jasminpatry/boostino/gaugeFg.c

#include "gaugeFg.h"

const uint16_t g_aNBbGaugeFg[] = { 10, 9, 311, 225 };
const uint8_t g_aBGaugeFg[] = {
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
};
