jasminpatry/boostino/labelAfr.c

#include "labelAfr.h"

const uint16_t g_aNBbLabelAfr[] = { 75, 9, 102, 21 };
const uint8_t g_aBLabelAfr[] = {
	0x0, 0x0, 0x0, 0x0, 0x1b, 0x66, 0x66, 0x2f, 0x0, 0x0, 0x0, 0x0, 0x2f, 0x66, 0x66, 0x66, 0x66, 0x66, 0x0, 0x55, 0x66, 0x66, 0x66, 0x66, 0x55, 0x0, 0x0,
	0x0, 0x0, 0x0, 0x0, 0xb6, 0xff, 0xff, 0x97, 0x0, 0x0, 0x0, 0x66, 0xf1, 0xff, 0xff, 0xff, 0xff, 0xff, 0x1b, 0xe3, 0xff, 0xff, 0xff, 0xff, 0xff, 0x87, 0x0,
	0x0, 0x0, 0x0, 0x43, 0xff, 0xf1, 0xff, 0xb6, 0x0, 0x0, 0x0, 0xd3, 0xff, 0xc5, 0x96, 0x97, 0x97, 0x87, 0x1b, 0xff, 0xff, 0x97, 0x97, 0xb6, 0xff, 0xf1, 0x0,
	0x0, 0x0, 0x0, 0xb6, 0xff, 0x87, 0xff, 0xd4, 0x0, 0x0, 0x1b, 0xff, 0xff, 0x43, 0x0, 0x0, 0x0, 0x0, 0x66, 0xff, 0xe2, 0x0, 0x0, 0x42, 0xff, 0xff, 0x1a,
	0x0, 0x0, 0x43, 0xff, 0xe3, 0x1a, 0xff, 0xff, 0x1a, 0x0, 0x42, 0xff, 0xff, 0x1b, 0x0, 0x0, 0x0, 0x0, 0x77, 0xff, 0xd3, 0x0, 0x0, 0x76, 0xff, 0xe3, 0x0,
	0x0, 0x0, 0xa6, 0xff, 0x87, 0x0, 0xe2, 0xff, 0x2f, 0x0, 0x66, 0xff, 0xff, 0xd4, 0xd4, 0xd4, 0xa6, 0x0, 0x96, 0xff, 0xc5, 0x97, 0x97, 0xe2, 0xff, 0x97, 0x0,
	0x0, 0x1a, 0xf1, 0xf0, 0x1b, 0x1a, 0xd3, 0xff, 0x66, 0x0, 0x87, 0xff, 0xff, 0xff, 0xff, 0xff, 0x97, 0x0, 0xc4, 0xff, 0xff, 0xff, 0xff, 0xff, 0x97, 0x0, 0x0,
	0x0, 0x97, 0xff, 0xff, 0xff, 0xff, 0xff, 0xff, 0x87, 0x0, 0xa6, 0xff, 0x97, 0x1a, 0x1b, 0x1a, 0x0, 0x0, 0xd4, 0xff, 0x87, 0x66, 0xf1, 0xff, 0x42, 0x0, 0x0,
	0x1a, 0xf0, 0xff, 0xd3, 0xd4, 0xd4, 0xe2, 0xff, 0x97, 0x0, 0xd4, 0xff, 0x77, 0x0, 0x0, 0x0, 0x0, 0x1a, 0xff, 0xff, 0x2f, 0x0, 0xb6, 0xff, 0x87, 0x0, 0x0,
	0x97, 0xff, 0xb5, 0x0, 0x0, 0x0, 0x87, 0xff, 0xd3, 0x0, 0xf1, 0xff, 0x55, 0x0, 0x0, 0x0, 0x0, 0x55, 0xff, 0xf1, 0x0, 0x0, 0x87, 0xff, 0xc5, 0x0, 0x0,
	0xf0, 0xff, 0x43, 0x0, 0x0, 0x0, 0x66, 0xff, 0xe2, 0x1b, 0xff, 0xff, 0x1a, 0x0, 0x0, 0x0, 0x0, 0x66, 0xff, 0xd4, 0x0, 0x0, 0x42, 0xff, 0xff, 0x1b, 0x0,
	0x1b, 0x1b, 0x0, 0x0, 0x0, 0x0, 0x0, 0x1b, 0x1a, 0x0, 0x1b, 0x1a, 0x0, 0x0, 0x0, 0x0, 0x0, 0x0, 0x1b, 0x0, 0x0, 0x0, 0x0, 0x1a, 0x1b, 0x0, 0x0,
};
