jasminpatry/boostino/labelMph.c

#include "labelMph.h"

const uint16_t g_aNBbLabelMph[] = { 71, 9, 102, 21 };
const uint8_t g_aBLabelMph[] = {
	0x0, 0x0, 0x0, 0x66, 0x66, 0x0, 0x0, 0x0, 0x0, 0x1b, 0x66, 0x54, 0x0, 0x0, 0x55, 0x66, 0x66, 0x66, 0x66, 0x55, 0x0, 0x0, 0x1a, 0x66, 0x54, 0x0, 0x0, 0x0, 0x1b, 0x66, 0x54, 
	0x0, 0x0, 0x66, 0xff, 0xff, 0x1a, 0x0, 0x0, 0x0, 0xb6, 0xff, 0xd4, 0x0, 0x0, 0xe2, 0xff, 0xff, 0xff, 0xff, 0xff, 0xa7, 0x0, 0x87, 0xff, 0xd3, 0x0, 0x0, 0x0, 0x87, 0xff, 0xc5, 
	0x0, 0x0, 0xa6, 0xff, 0xff, 0x65, 0x0, 0x0, 0x43, 0xff, 0xff, 0x97, 0x0, 0x1b, 0xff, 0xff, 0x97, 0x97, 0xb5, 0xff, 0xff, 0x1b, 0x97, 0xff, 0x97, 0x0, 0x0, 0x0, 0x97, 0xff, 0x97, 
	0x0, 0x0, 0xd4, 0xff, 0xff, 0x76, 0x0, 0x0, 0xb6, 0xff, 0xff, 0x97, 0x0, 0x66, 0xff, 0xe2, 0x0, 0x0, 0x1b, 0xff, 0xff, 0x1b, 0xd4, 0xff, 0x87, 0x0, 0x0, 0x0, 0xd3, 0xff, 0x76, 
	0x0, 0x42, 0xff, 0xe2, 0xff, 0x97, 0x0, 0x1b, 0xf1, 0xf0, 0xff, 0x97, 0x0, 0x77, 0xff, 0xd4, 0x0, 0x0, 0x42, 0xff, 0xff, 0x1b, 0xd4, 0xff, 0x65, 0x1b, 0x1b, 0x1a, 0xe2, 0xff, 0x66, 
	0x0, 0x87, 0xff, 0xb6, 0xff, 0xb5, 0x0, 0x97, 0xf1, 0xa6, 0xff, 0x96, 0x0, 0x97, 0xff, 0xa7, 0x1a, 0x30, 0xa7, 0xff, 0xc5, 0x1a, 0xff, 0xff, 0xff, 0xff, 0xff, 0xff, 0xff, 0xff, 0x1b, 
	0x0, 0xc5, 0xff, 0x87, 0xd4, 0xd4, 0x1b, 0xf0, 0xb6, 0x96, 0xff, 0x97, 0x0, 0xc5, 0xff, 0xff, 0xff, 0xff, 0xff, 0xff, 0x66, 0x54, 0xff, 0xf0, 0xd3, 0xd3, 0xd4, 0xd4, 0xff, 0xe2, 0x0, 
	0x0, 0xf1, 0xff, 0x30, 0xd3, 0xf1, 0x87, 0xff, 0x43, 0x97, 0xff, 0x97, 0x0, 0xd4, 0xff, 0xc5, 0xd4, 0xd3, 0xc5, 0x65, 0x0, 0x77, 0xff, 0xd4, 0x0, 0x0, 0x0, 0x77, 0xff, 0xd4, 0x0, 
	0x55, 0xff, 0xd3, 0x0, 0xa6, 0xff, 0xe3, 0xc5, 0x0, 0xc5, 0xff, 0x77, 0x1a, 0xff, 0xff, 0x2f, 0x0, 0x0, 0x0, 0x0, 0x0, 0x97, 0xff, 0xa7, 0x0, 0x0, 0x0, 0x97, 0xff, 0x97, 0x0, 
	0x97, 0xff, 0xa6, 0x0, 0x97, 0xff, 0xff, 0x77, 0x0, 0xd4, 0xff, 0x66, 0x54, 0xff, 0xf1, 0x0, 0x0, 0x0, 0x0, 0x0, 0x0, 0xc5, 0xff, 0x87, 0x0, 0x0, 0x0, 0xc4, 0xff, 0x87, 0x0, 
	0xd4, 0xff, 0x66, 0x0, 0x76, 0xff, 0xe3, 0x0, 0x0, 0xd3, 0xff, 0x66, 0x66, 0xff, 0xd4, 0x0, 0x0, 0x0, 0x0, 0x0, 0x0, 0xd4, 0xff, 0x66, 0x0, 0x0, 0x0, 0xd3, 0xff, 0x66, 0x0, 
	0x1b, 0x1b, 0x0, 0x0, 0x0, 0x1b, 0x0, 0x0, 0x0, 0x0, 0x1a, 0x0, 0x0, 0x1b, 0x0, 0x0, 0x0, 0x0, 0x0, 0x0, 0x0, 0x0, 0x1b, 0x0, 0x0, 0x0, 0x0, 0x1a, 0x1b, 0x0, 0x0, 
};
